ddanila/juku/bottom-case/projection-xy.scad

use <juku-bottom-case.scad>

projection(cut = false)
    bottom_case();
