ddanila/juku/keycap/juku-keycap.scad

// Juku keycap
// Units: millimeters

outside_width = 17.0;
outside_depth = 17.0;
height = 10;
top_chamfer_z = 4;
top_chamfer_xy = 3;
wall_thickness = 0.80;
top_thickness = 3;
chamfer_steps = 128;
top_dish_radius = 100;
top_dish_depth = 1;
top_dish_z_offset = 0.5;
top_dish_segments = 2048;
spring_rod_diameter = 2.25;
spring_rod_length = 2;
spring_rod_end_chamfer = 0.5;
spring_rod_base_width = 2.25;
spring_rod_base_depth = 8;
spring_rod_base_height = 2;
spring_rod_base_xy_chamfer = 1;
contact_pusher_diameter = 2.5;
contact_pusher_edge_spacing = 5;
contact_pusher_wall_overlap = 0.05;
latch_width = 7;
latch_thickness = wall_thickness;
latch_length = 2;
latch_tooth_depth = 0.6;
latch_tooth_height = 1.2;
latch_tooth_z_offset = 1.2;
latch_side_round = 0.6;
latch_round_segments = 32;

inner_width = outside_width - 2 * wall_thickness;
inner_depth = outside_depth - 2 * wall_thickness;

$fn = 128;

function rounded_chamfer_inset(z, z_height, xy_inset) =
    xy_inset * (1 - sqrt(1 - (z / z_height) * (z / z_height)));

module thin_box(width, depth, z) {
    translate([0, 0, z])
        cube([width, depth, 0.01], center = true);
}

module rounded_chamfered_box(width, depth, total_height, chamfer_z, chamfer_xy) {
    body_z = total_height - chamfer_z;

    hull() {
        thin_box(width, depth, 0);
        thin_box(width, depth, body_z);
    }

    for (step = [0 : chamfer_steps - 1]) {
        z1 = chamfer_z * step / chamfer_steps;
        z2 = chamfer_z * (step + 1) / chamfer_steps;
        inset1 = rounded_chamfer_inset(z1, chamfer_z, chamfer_xy);
        inset2 = rounded_chamfer_inset(z2, chamfer_z, chamfer_xy);

        hull() {
            thin_box(width - 2 * inset1, depth - 2 * inset1, body_z + z1);
            thin_box(width - 2 * inset2, depth - 2 * inset2, body_z + z2);
        }
    }
}

module keycap_shell() {
    difference() {
        rounded_chamfered_box(
            outside_width,
            outside_depth,
            height,
            top_chamfer_z,
            top_chamfer_xy
        );

        translate([0, 0, (height - top_thickness) / 2 - 0.02])
            cube(
                [
                    inner_width,
                    inner_depth,
                    height - top_thickness + 0.04
                ],
                center = true
            );

        translate([0, 0, height + top_dish_radius - top_dish_depth + top_dish_z_offset])
            sphere(r = top_dish_radius, $fn = top_dish_segments);
    }
}

module spring_rod() {
    radius = spring_rod_diameter / 2;
    tip_radius = radius - spring_rod_end_chamfer;
    rod_top_z = height - top_thickness;
    straight_length = rod_top_z + spring_rod_length - spring_rod_end_chamfer;

    translate([0, 0, -spring_rod_length + spring_rod_end_chamfer])
        cylinder(h = straight_length, r = radius);

    translate([0, 0, -spring_rod_length])
        cylinder(h = spring_rod_end_chamfer, r1 = tip_radius, r2 = radius);
}

module rounded_xy_box(width, depth, z_height, xy_radius) {
    linear_extrude(height = z_height)
        offset(r = xy_radius)
            square([width - 2 * xy_radius, depth - 2 * xy_radius], center = true);
}

module spring_rod_base() {
    translate([0, 0, height - top_thickness - spring_rod_base_height])
        rounded_xy_box(
            spring_rod_base_width,
            spring_rod_base_depth,
            spring_rod_base_height,
            spring_rod_base_xy_chamfer
        );
}

module contact_pushers() {
    radius = contact_pusher_diameter / 2;
    center_spacing = contact_pusher_diameter + contact_pusher_edge_spacing;
    y = inner_depth / 2 - radius + contact_pusher_wall_overlap;
    wall_projection = inner_depth / 2 - y + contact_pusher_wall_overlap;
    rod_height = height - top_thickness;

    for (x = [-center_spacing / 2, center_spacing / 2]) {
        translate([x, y, 0])
            contact_pusher_shape(radius, wall_projection, rod_height);
    }
}

module contact_pusher_shape(radius, wall_projection, z_height) {
    linear_extrude(height = z_height)
        union() {
            intersection() {
                circle(r = radius);
                translate([0, -radius / 2])
                    square([2 * radius, radius], center = true);
            }

            translate([0, wall_projection / 2])
                square([2 * radius, wall_projection], center = true);
        }
}

module latch(side) {
    x = side * (outside_width / 2 - latch_thickness / 2);
    tooth_z = -latch_length + latch_tooth_height - latch_tooth_z_offset;

    translate([x, 0, -latch_length / 2])
        rounded_latch_plate(latch_width, latch_length, latch_thickness, latch_side_round);

    intersection() {
        translate([
            x - side * latch_thickness / 2,
            0,
            tooth_z
        ])
            rotate([90, 0, 0])
                linear_extrude(height = latch_width, center = true)
                    polygon([
                        [0, 0],
                        [-side * latch_tooth_depth, latch_tooth_height / 2],
                        [0, latch_tooth_height]
                    ]);

        translate([0, 0, tooth_z + latch_tooth_height / 2])
            rounded_yz_prism(
                latch_width,
                latch_tooth_height,
                outside_width + 2 * latch_tooth_depth,
                latch_side_round
            );
    }
}

module rounded_latch_plate(width, length, thickness, radius) {
    rounded_yz_prism(width, length, thickness, radius);
}

module rounded_yz_prism(width, length, thickness, radius) {
    multmatrix([
        [0, 0, 1, 0],
        [1, 0, 0, 0],
        [0, 1, 0, 0],
        [0, 0, 0, 1]
    ])
        linear_extrude(height = thickness, center = true)
            rounded_latch_yz_profile(width, length, radius);
}

function arc_points(cx, cy, radius, start_angle, end_angle, steps) = [
    for (i = [0 : steps])
        [
            cx + radius * cos(start_angle + (end_angle - start_angle) * i / steps),
            cy + radius * sin(start_angle + (end_angle - start_angle) * i / steps)
        ]
];

module rounded_latch_yz_profile(width, length, radius) {
    r = min(radius, min(width, length) / 2);

    polygon(concat(
        [
            [-width / 2,  length / 2],
            [ width / 2,  length / 2],
            [ width / 2, -length / 2 + r]
        ],
        arc_points(width / 2 - r, -length / 2 + r, r, 0, -90, latch_round_segments),
        [
            [-width / 2 + r, -length / 2]
        ],
        arc_points(-width / 2 + r, -length / 2 + r, r, -90, -180, latch_round_segments)
    ));
}

module latches() {
    latch(1);
    latch(-1);
}

union() {
    keycap_shell();
    spring_rod_base();
    spring_rod();
    contact_pushers();
    latches();
}
